AzidoPP/STM-C4/Ver4.0/Keil_proj/c4/hardware/LED.h

#ifndef LED_H
#define LED_H

#include "stm32f10x.h"
#include "config.h"
#include <stdint.h>

void LED_Init(void);
uint16_t LED_GetPwmMax(void);
void LED_SetColor(uint16_t red, uint16_t green);
void LED_SetRed(uint16_t red);
void LED_SetGreen(uint16_t green);
void LED_SetYellow(uint16_t level);
void LED_AllOff(void);

void Relay_On(void);
void Relay_Off(void);

void Buzzer_Init(void);
void Buzzer_SetFreq(uint32_t freq_hz);
void Buzzer_SetDuty(uint8_t duty_pct);
void Buzzer_On(void);
void Buzzer_Off(void);

#endif
