AzidoPP/STM-C4/Ver4.0/Keil_proj/c4/hardware/Serial.c

#include "Serial.h"

void Serial_Init(void)
{
	RCC_APB2PeriphClockCmd(RCC_APB2Periph_USART1, ENABLE);
	RCC_APB2PeriphClockCmd(RCC_APB2Periph_GPIOA, ENABLE);

	GPIO_InitTypeDef gpio;
	gpio.GPIO_Mode = GPIO_Mode_AF_PP;
	gpio.GPIO_Pin = GPIO_Pin_9;
	gpio.GPIO_Speed = GPIO_Speed_50MHz;
	GPIO_Init(GPIOA, &gpio);

	USART_InitTypeDef usart;
	usart.USART_BaudRate = 9600;
	usart.USART_HardwareFlowControl = USART_HardwareFlowControl_None;
	usart.USART_Mode = USART_Mode_Tx;
	usart.USART_Parity = USART_Parity_No;
	usart.USART_StopBits = USART_StopBits_1;
	usart.USART_WordLength = USART_WordLength_8b;
	USART_Init(USART1, &usart);

	USART_Cmd(USART1, ENABLE);
}

void Serial_SendByte(uint8_t Byte)
{
	USART_SendData(USART1, Byte);
	while (USART_GetFlagStatus(USART1, USART_FLAG_TXE) == RESET)
	{
	}
}

void Serial_SendArray(uint8_t *Array, uint16_t Length)
{
	uint16_t i;
	for (i = 0; i < Length; i++)
	{
		Serial_SendByte(Array[i]);
	}
}
